Feinmechaniker/pico-sdr/04_LTSpice/BP_1.asc

C1: cap; 1.600n
C3: cap; 1.600n
L2: ind; 8.200µ
RL: res; 50
V1: voltage; ""; AC 1 0; Rser=50.00
Named nets: 0
.ac dec 1001 100k 45Meg
.net I(RL) V1
3rd Order Butterworth Lowpass
Shunt First
Cutoff Frequency = 2 MHz


rf-tools.com | May 16 2025 18:30
