Feinmechaniker/pico-sdr/04_LTSpice/BP_2.asc

C1: cap; 2.400n
C2: cap; 1.800n
C3: cap; 2.400n
L1: ind; 2.200µ
L2: ind; 3.300µ
L3: ind; 2.200µ
RL: res; 50
V1: voltage; ""; AC 1 0; Rser=50.00
Named nets: 0
.ac dec 1001 100k 45Meg
.net I(RL) V1
3rd Order Butterworth Bandpass
Conventional, Series First
Lower Cutoff Freq. = 1 MHz; Upper Cutoff Freq. = 4.5 MHz


rf-tools.com | May 16 2025 17:12
