Feinmechaniker/pico-sdr/04_LTSpice/BP_3.asc

C1: cap; 510.0p
C2: cap; 1.300n
C3: cap; 510.0p
L1: ind; 1.500µ
L2: ind; 680.0n
L3: ind; 1.500µ
RL: res; 50
V1: voltage; ""; AC 1 0; Rser=50.00
Named nets: 0
.ac dec 1001 100k 45Meg
.net I(RL) V1
3rd Order Butterworth Bandpass
Conventional, Series First
Lower Cutoff Freq. = 3.5 MHz; Upper Cutoff Freq. = 8.5 MHz


rf-tools.com | May 16 2025 18:22
