Feinmechaniker/pico-sdr/04_LTSpice/BP_4.asc

C1: cap; 270.0p
C2: cap; 680.0p
C3: cap; 270.0p
L1: ind; 820.0n
L2: ind; 330.0n
L3: ind; 820.0n
RL: res; 50
V1: voltage; ""; AC 1 0; Rser=50.00
Named nets: 0
.ac dec 1001 100k 45Meg
.net I(RL) V1
3rd Order Butterworth Bandpass
Conventional, Series First
Lower Cutoff Freq. = 7 MHz; Upper Cutoff Freq. = 16 MHz


rf-tools.com | May 16 2025 19:22
