Feinmechaniker/pico-sdr/04_LTSpice/QSD_Simulation.asc

C1: cap; 27pF
C2: cap; 10n
C3: cap; 10n
C4: cap; 10µ
C5: cap; 10µ
C6: cap; 27pF
C7: cap; 10n
C8: cap; 10n
C9: cap; 10µ
C10: cap; 220n
C11: cap; 220n
L1: ind2; 50µH
L2: ind2; 50µH
L3: ind2; 50µH
L4: ind; 33µH
L5: ind; 33µH
R1: res; 100k
R2: res; 100
R3: res; 100
R6: res; 100k
S1: sw; MYSW
S2: sw; MYSW
S3: sw; MYSW
S4: sw; MYSW
U1: LT6231
V1: voltage; 3.3
V2: voltage; SINE(0 10u {HF}); Rser=50
V3: voltage; PULSE(0 1 0 0.001p 0.001p {SW_time} {4*SW_time})
V5: voltage; 1.65
V6: voltage; PULSE(0 1 {2*SW_time} 0.001p 0.001p {SW_time} {4*SW_time})
Named nets: 0, V_0_deg, V_180_deg, Vcc, I1, BIAS, 10, 01
.model MYSW SW(Vt=0.9 Vh=0 Ron=3 Roff=100Meg)
.tran 100u 250u 40u 5m
.param HF=15Meg LO_freq={HF -NF} LO_period={1/LO_freq} SW_time={LO_period/4}
Signals for voltage-controlled switches used to simulate our multiplexer.
Tayloe-Mixer
Simulation Control
.param NF 10000
RF signal in
low-pass 2nd order
cut-off 277 KHz
K L1 L2 L3 1.0
BW = 150 kHz
low-pass
cut-off 48 KHz
Gain 60 dB
Quadrature Sampling Detector | Tayloe Mixer
Joe G. (DL3AKB)
Only the I branch Q is identical
